khimscho/NEMO/LoggerFirmware/include/PointBridge.h

/*! \file PointBridge.h
 *  \brief Simple UDP broadcast bridge to NMEA0183
 *
 * Under exceptional circumstances, it might be interesting to capture UDP traffic of NMEA
 * strings on the WiFi, given a broadcast port, and send them to the NMEA0183 hardware
 * outputs (if available and enabled).  In this implementation, anything sent to the
 * configured port is echoed to the first NMEA0183 channel without checking --- the messages
 * must therefore be good as is!
 *
 * Copyright (c) 2021, University of New Hampshire, Center for Coastal and Ocean Mapping.
 *
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
 * THE SOFTWARE IS PROVIDED "AS IS", WITHOUT WARRANTY OF ANY KIND, EXPRESS OR
 * IMPLIED, INCLUDING BUT NOT LIMITED TO THE WARRANTIES OF MERCHANTABILITY, FITNESS
 * FOR A PARTICULAR PURPOSE AND NONINFRINGEMENT. IN NO EVENT SHALL THE AUTHORS
 * OR COPYRIGHT HOLDERS BE LIABLE FOR ANY CLAIM, DAMAGES OR OTHER LIABILITY,
 * WHETHER IN AN ACTION OF CONTRACT, TORT OR OTHERWISE, ARISING FROM, OUT OF
 * OR IN CONNECTION WITH THE SOFTWARE OR THE USE OR OTHER DEALINGS IN THE SOFTWARE.
 */

#ifndef __POINT_BRIDGE_H__
#define __POINT_BRIDGE_H__

#include <stdint.h>
#include "Arduino.h"
#include "AsyncUDP.h"

namespace nmea {
namespace N0183 {

/// \class PointBridge
/// \brief Use the asynchronous UDP facilities to capture broadcast packets in the background
///
/// Under certain circumstances, it may be necessary to capture UDP packets on the WiFi network
/// that contain NMEA0183 messages, and then pass them on to the transmitters on the WIBL board
/// so that the system can act as a network bridge (e.g., to provide data where a NMEA0183 feed
/// isn't available, as on many research ships).  This object provides the means to run a thread
/// in the background to do this, handling packets as they arrive.

class PointBridge {
public:
    /// \brief Default constructor, with RAII implementation for the bridge
    PointBridge(void);
    /// \brief Default destructor, with brings down the bridge
    ~PointBridge(void);

    /// \brief Set the verbosity of message reporting during capture on the bridge
    void SetVerbose(bool state);
private:
    AsyncUDP    *m_bridge;  ///< Pointer to the control object for the background capture thread
    bool        m_verbose;  ///< Flag: True => print more information, False => quiet mode

    /// \brief Call-back method to extract the NMEA strings from the UDP packet and write them to the transmitters
    void HandlePacket(AsyncUDPPacket& packet);
};

}
}

#endif
