khimscho/NEMO/LoggerFirmware/src/SupplyMonitor.cpp

/*!\file SupplyMonitor.cpp
 * \brief Interface for NEMO-30 power monitoring
 *
 * The NEMO-30 variant of the logger has the ability to monitor the input power feed
 * so that it can detect when the emergency backup power has kicked in, and therefore
 * turn off the logging for a safe shutdown before it gives out.
 *
 * Copyright (c) 2021, University of New Hampshire, Center for Coastal and Ocean Mapping.
 *
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
 * THE SOFTWARE IS PROVIDED "AS IS", WITHOUT WARRANTY OF ANY KIND, EXPRESS OR
 * IMPLIED, INCLUDING BUT NOT LIMITED TO THE WARRANTIES OF MERCHANTABILITY, FITNESS
 * FOR A PARTICULAR PURPOSE AND NONINFRINGEMENT. IN NO EVENT SHALL THE AUTHORS
 * OR COPYRIGHT HOLDERS BE LIABLE FOR ANY CLAIM, DAMAGES OR OTHER LIABILITY,
 * WHETHER IN AN ACTION OF CONTRACT, TORT OR OTHERWISE, ARISING FROM, OUT OF
 * OR IN CONNECTION WITH THE SOFTWARE OR THE USE OR OTHER DEALINGS IN THE SOFTWARE.
 */

#include <Arduino.h>
#include "SupplyMonitor.h"
#include "Configuration.h"

namespace logger {

/// If configured, bring up the power supply monitoring code, using the given pin.  The code
/// checks the voltage on the supplied pin, and expects it to stay at least above the half-supply
/// level, or it sounds the alarm.
///
/// \param monitor_pin  GPIO pin number to use for monitoring

SupplyMonitor::SupplyMonitor(uint8_t monitor_pin)
: m_monitorPower(false), m_monitorPin(monitor_pin)
{
    if (!logger::LoggerConfig.GetConfigBinary(logger::Config::ConfigParam::CONFIG_POWMON_B, m_monitorPower)) {
        // Returns false if the key doesn't exist.  This usually means that
        // it hasn't been set yet, and that means we're still in programming,
        // or debugging mode.  In that mode, the power monitoring doesn't work
        // (there's no input power to monitor!), so we turn monitoring off.
        m_monitorPower = false;
    }
    if (m_monitorPower) {
        pinMode(m_monitorPin, INPUT);
        uint16_t v;
        EmergencyPower(&v);
        Serial.printf("DBG: monitor voltage level = %hu\n", v);
    }
}

/// Check the emergency power pin to see whether the main power supply is on.  The code assumes that
/// all is well so long as the voltage on the input pin is at least half the full range of the converter
/// (i.e., 3.3V/2 = 1.65V).
///
/// \param value    Pointer to where to store the value read from the ADC, or nullptr if you don't need it
/// \return True if the module need to switch to emergency power, or False if the main power is on

bool SupplyMonitor::EmergencyPower(uint16_t *value)
{
    if (m_monitorPower) {
        uint16_t monitor_voltage = analogRead(m_monitorPin);
        if (value != nullptr)
            *value = monitor_voltage;
        if (monitor_voltage < 2048)
            return true;
    }
    return false;
}

}
