khimscho/NEMO/Tools/plot_motion_data.py

## @file plot_motion_data.py
# @brief Driver to read and plot motion data from the logger file.
#
# Copyright 2021 Center for Coastal and Ocean Mapping & NOAA-UNH Joint
# Hydrographic Center, University of New Hampshire.
#
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
import sys
import wibl.core.logger_file as LoggerFile
import matplotlib.pyplot as plt
import numpy as np

file = open(sys.argv[1], 'rb')

times = []
acc = []
gyro = []
temp = []

packet_count = 0
motion_count = 0

source = LoggerFile.PacketFactory(file)
accel_scale = 0
gyro_scale = 0
temp_scale = 0
temp_offset = 0

while source.has_more():
    pkt = source.next_packet()
    if pkt is not None:
        packet_count += 1
        if isinstance(pkt, LoggerFile.Motion) or isinstance(pkt, LoggerFile.RawIMU):
            if isinstance(pkt, LoggerFile.RawIMU):
                if accel_scale == 0:
                    print('ERR: scales not set; was there a scales metadata element?')
                    sys.exit(1)
                accel_pt = (pkt.accel[0] * accel_scale, pkt.accel[1] * accel_scale, pkt.accel[2] * accel_scale, np.sqrt(pkt.accel[0]**2 + pkt.accel[1]**2 + pkt.accel[2]**2) * accel_scale)
                gyro_pt = (pkt.gyro[0] * gyro_scale, pkt.gyro[1] * gyro_scale, pkt.gyro[2] * gyro_scale)
                temp_pt = (pkt.temp * temp_scale) + temp_offset
            else:
                accel_pt = (pkt.accel[0], pkt.accel[1], pkt.accel[2], np.sqrt(pkt.accel[0]**2 + pkt.accel[1]**2 + pkt.accel[2]**2))
                gyro_pt = pkt.gyro
                temp_pt = pkt.temp
            motion_count += 1
            times.append(pkt.elapsed / 1000)
            acc.append(accel_pt)
            gyro.append(gyro_pt)
            temp.append(temp_pt)
        elif isinstance(pkt, LoggerFile.SensorScales):
            try:
                accel_scale = 1.0 / pkt.config['imu']['recipAccelScale']
                gyro_scale = 1.0 / pkt.config['imu']['recipGyroScale']
                temp_scale = 1.0 / pkt.config['imu']['recipTempScale']
                temp_offset = pkt.config['imu']['tempOffset']
            except KeyError as e:
                print('ERR: bad key error')
                sys.exit(1)

print("Found " + str(packet_count) + " packets total")
print("Found " + str(motion_count) + " motion packets")

plt.figure(figsize=(14,10))

plt.subplot(3,1,1)
plt.plot(times, temp)
plt.grid()
plt.xlabel('Elapsed Time (s)')
plt.ylabel('Sensor Temperature (deg. C)')

plt.subplot(3,1,2)
plt.plot(times, acc)
plt.grid()
plt.xlabel('Elapsed Time (s)')
plt.ylabel('Accelerations (G)')
plt.legend(('X-Axis', 'Y-Axis', 'Z-Axis', 'Magnitude'))

plt.subplot(3,1,3)
plt.plot(times, gyro)
plt.grid()
plt.xlabel('Elapsed Time (s)')
plt.ylabel('Rotation Rate (deg/s)')
plt.legend(('X-Axis', 'Y-Axis', 'Z-Axis'))

plt.show()
